servernoj/cheroma/CAD/OpenSCAD/P1.stl

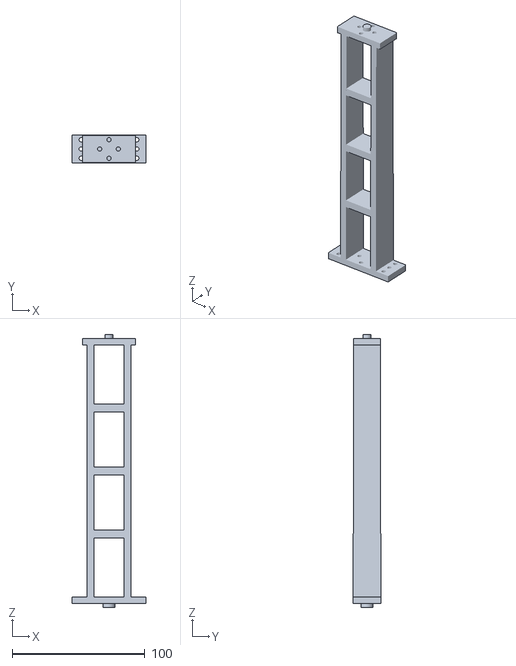
[picture p16: CAD file, 2026-01-05]
CAD/OpenSCAD/P1.stl
56.0 x 21.0 x 206.0
