servernoj/cheroma/CAD/FreeCAD/pieces/hollow/pieces-bishop.stl

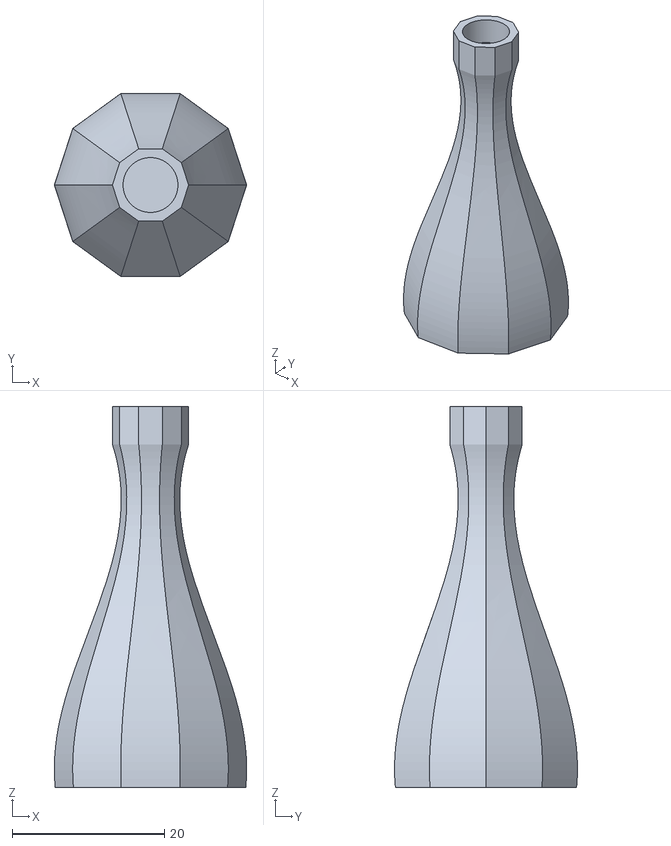
[picture p17: CAD file, 2026-03-28]
CAD/FreeCAD/pieces/hollow/pieces-bishop.stl
25.2 x 24.0 x 50.0
