servernoj/cheroma/CAD/FreeCAD/pieces/solid/pieces-pawn.stl

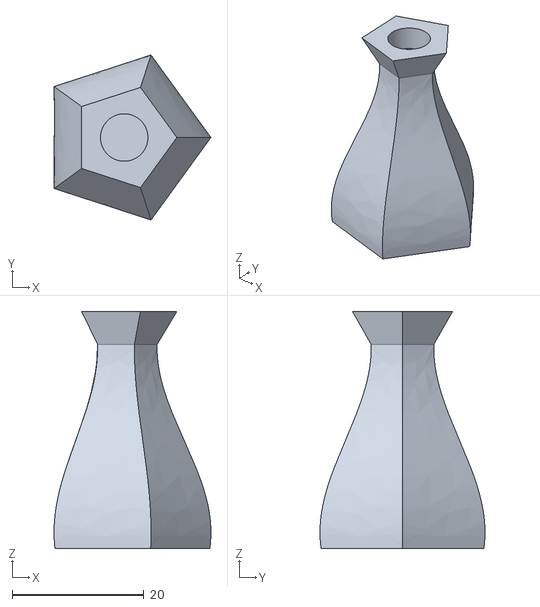
[picture p18: CAD file, 2026-03-25]
CAD/FreeCAD/pieces/solid/pieces-pawn.stl
23.8 x 25.1 x 36.0
