servernoj/cheroma/CAD/OpenSCAD/P3.stl

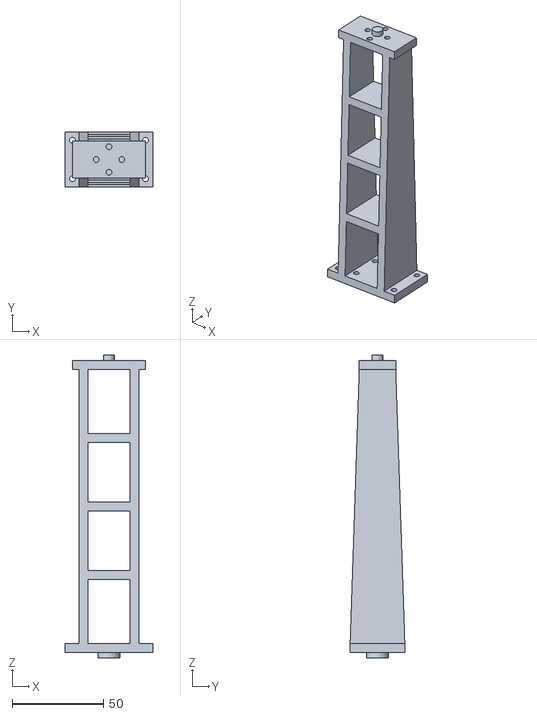
[picture p19: CAD file, 2026-01-05]
CAD/OpenSCAD/P3.stl
48.0 x 30.0 x 166.0
