servernoj/cheroma/CAD/FreeCAD/pieces/hollow/pieces-king.stl

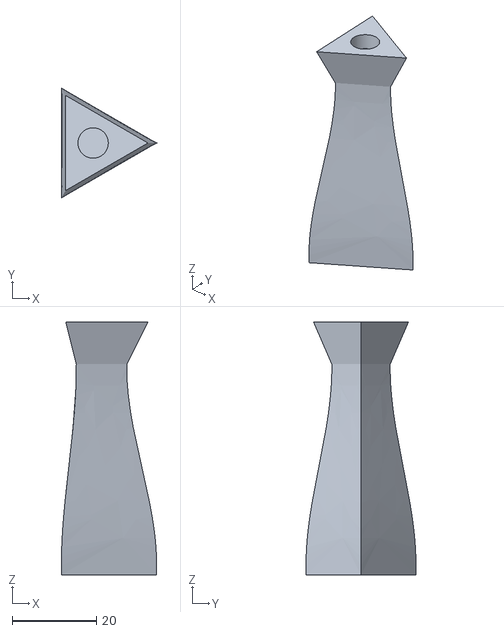
[picture p20: CAD file, 2026-03-28]
CAD/FreeCAD/pieces/hollow/pieces-king.stl
22.6 x 26.1 x 60.0
