servernoj/cheroma/CAD/FreeCAD/pieces/solid/pieces-rook.stl

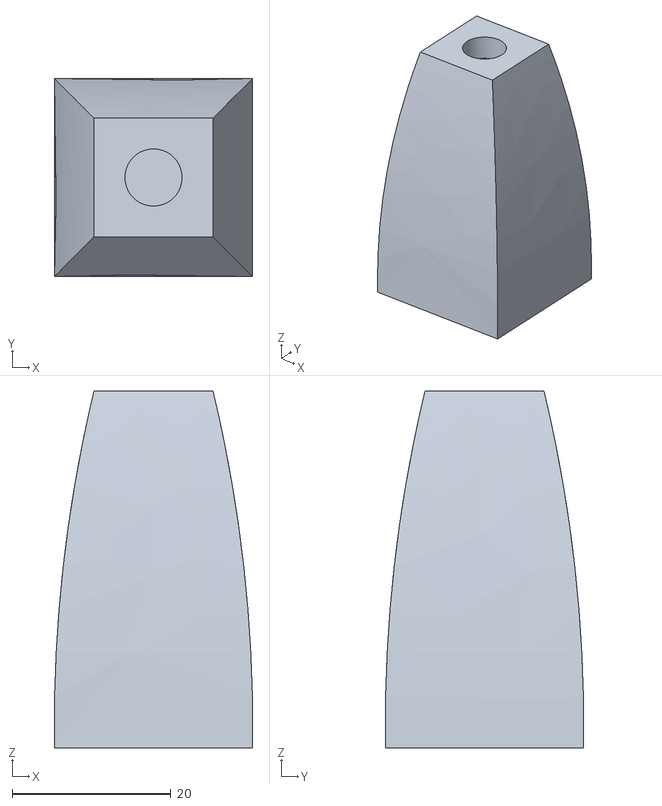
[picture p21: CAD file, 2026-03-25]
CAD/FreeCAD/pieces/solid/pieces-rook.stl
25.0 x 25.0 x 45.0
