servernoj/cheroma/apps/api/src/gpio-stub.js

/**
 * GPIO stub: real @bratbit/onoff on Linux, no-op mock elsewhere (e.g. macOS).
 * Use this instead of importing @bratbit/onoff directly so the app runs without
 * native GPIO on non-Linux.
 * When using real onoff, call Gpio.setChipRegex(regex) before new Gpio(...) to override chip detection.
 */
import os from 'os'

let Gpio

/** Mock Gpio: constructor and methods no-op, no native dependency */
class MockGpio {
  constructor(_gpio, _direction, _edge, _options) { }
  static setChipRegex(_regex) { }
  watch(_callback) { }
  unwatchAll() { }
  close() { }
  get unexport() {
    return this.close.bind(this)
  }
}

if (os.platform() === 'linux') {
  try {
    const onoff = await import('@bratbit/onoff')
    Gpio = onoff.Gpio
  } catch (e) {
    Gpio = MockGpio
    console.error(e.message)
  }
} else {
  Gpio = MockGpio
}

export { Gpio }
